johnwargo/word-clock-neomatrix-wifi-desktop/word-clock-neomatrix-wifi-desktop/moon.ino

/*
  Adapted from phil b's TIMESQUARE WATCH code.

  Only here if you feel like it!

*/

// Moon display: shows APPROXIMATE phase of moon.  This is not a medical
// device -- do not rely on this data if you are prone to lycanthropy.
// The phase shown is based on time elapsed since a known new moon, an
// approach that the Arduino can easily process but may be limited by a
// few flaws: the "known new moon" time is based on UTC, not local time,
// and may be a few hours off; the lunar period is assumed uniform and
// is rounded to whole seconds, and thus may drift over very long periods;
// unknown long-term accuracy of RTClib (e.g. DST & leap seconds ignored);
// uses 32-bit unixtime() and thus likely innacurate in years 2038+.
// This is for fun, not Real Science(tm).

// Used by various display modes for smooth fade-out before sleep
const uint8_t PROGMEM
fade[] =
{
  0,  1,  1,  2,  4,  5,  8, 10, 13, 17, 22, 27, 32, 39, 46,
  53, 62, 71, 82, 93, 105, 117, 131, 146, 161, 178, 196, 214, 234, 255
};

static const uint8_t PROGMEM
phases[] = {
  0x3B, 0x1F, 0x01, 0x00, 0x3E, 0x26, 0x03, 0x00, 0x3F, 0x2E, 0x06, 0x00, 0x42, 0x3E, 0x07,
  0x00, 0x47, 0x56, 0x07, 0x00, 0x54, 0x7A, 0x07, 0x00, 0x81, 0x88, 0x07, 0x00, 0xCC, 0x88,
  0x07, 0x00, 0xF2, 0x88, 0x07, 0x00, 0xF2, 0x84, 0x06, 0x00, 0xF0, 0x77, 0x03, 0x00, 0xED,
  0x63, 0x01, 0x00, 0xE3, 0x42, 0x01, 0x00, 0xCE, 0x27, 0x01, 0x00, 0x96, 0x1E, 0x01, 0x00,
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
      if (clr > 0 && clr < 70) {
        clr = clr * 40;  // boost dim pixels
      }
      matrix.drawPixel(dx + x, dy + y,
                       matrix.Color(0, 0, clr)); // draw in blue, pale white pixels look green and funky...

    }
  }
}
