johnwargo/word-clock-neomatrix-wifi-desktop/word-clock-neomatrix-wifi-desktop/adjust-brightness.ino

// change brightness based on the time of day.

void adjustBrightness(DateTime theTime) {

  // get time from the RTC
  //DateTime thetime = RTC.now();
  
  //change brightness if it's night time
  if (theTime.hour() < MORNINGCUTOFF || theTime.hour() > NIGHTCUTOFF) {
    matrix.setBrightness(NIGHTBRIGHTNESS);
  } else {
    matrix.setBrightness(DAYBRIGHTNESS);
  }
}
